charlee/LedMatrixClock2024/LedMatrixClock2024/include/config.h

#ifndef __CONFIG_H__
#define __CONFIG_H__

// WIFI SSID and password
#define WIFI_SSID ""
#define WIFI_PASSWORD ""

// time server that returns ISO 8601 formatted time, in text/plain
// example request and response:
//
// GET / HTTP/1.1
//
// Content-Type: text/plain
//
// YYYY-MM-DDTHH:MM:SS.uuuuuuuuu+ZZ:ZZ
#define TIME_SERVER ""

#endif
